ScatteredDrifter/Monorail-cut/pcb_source/Monorail_Steam_Reduced.kicad_sch

## KiCad design pcb_source/Monorail_Steam_Reduced.kicad_sch (2023-11-18)

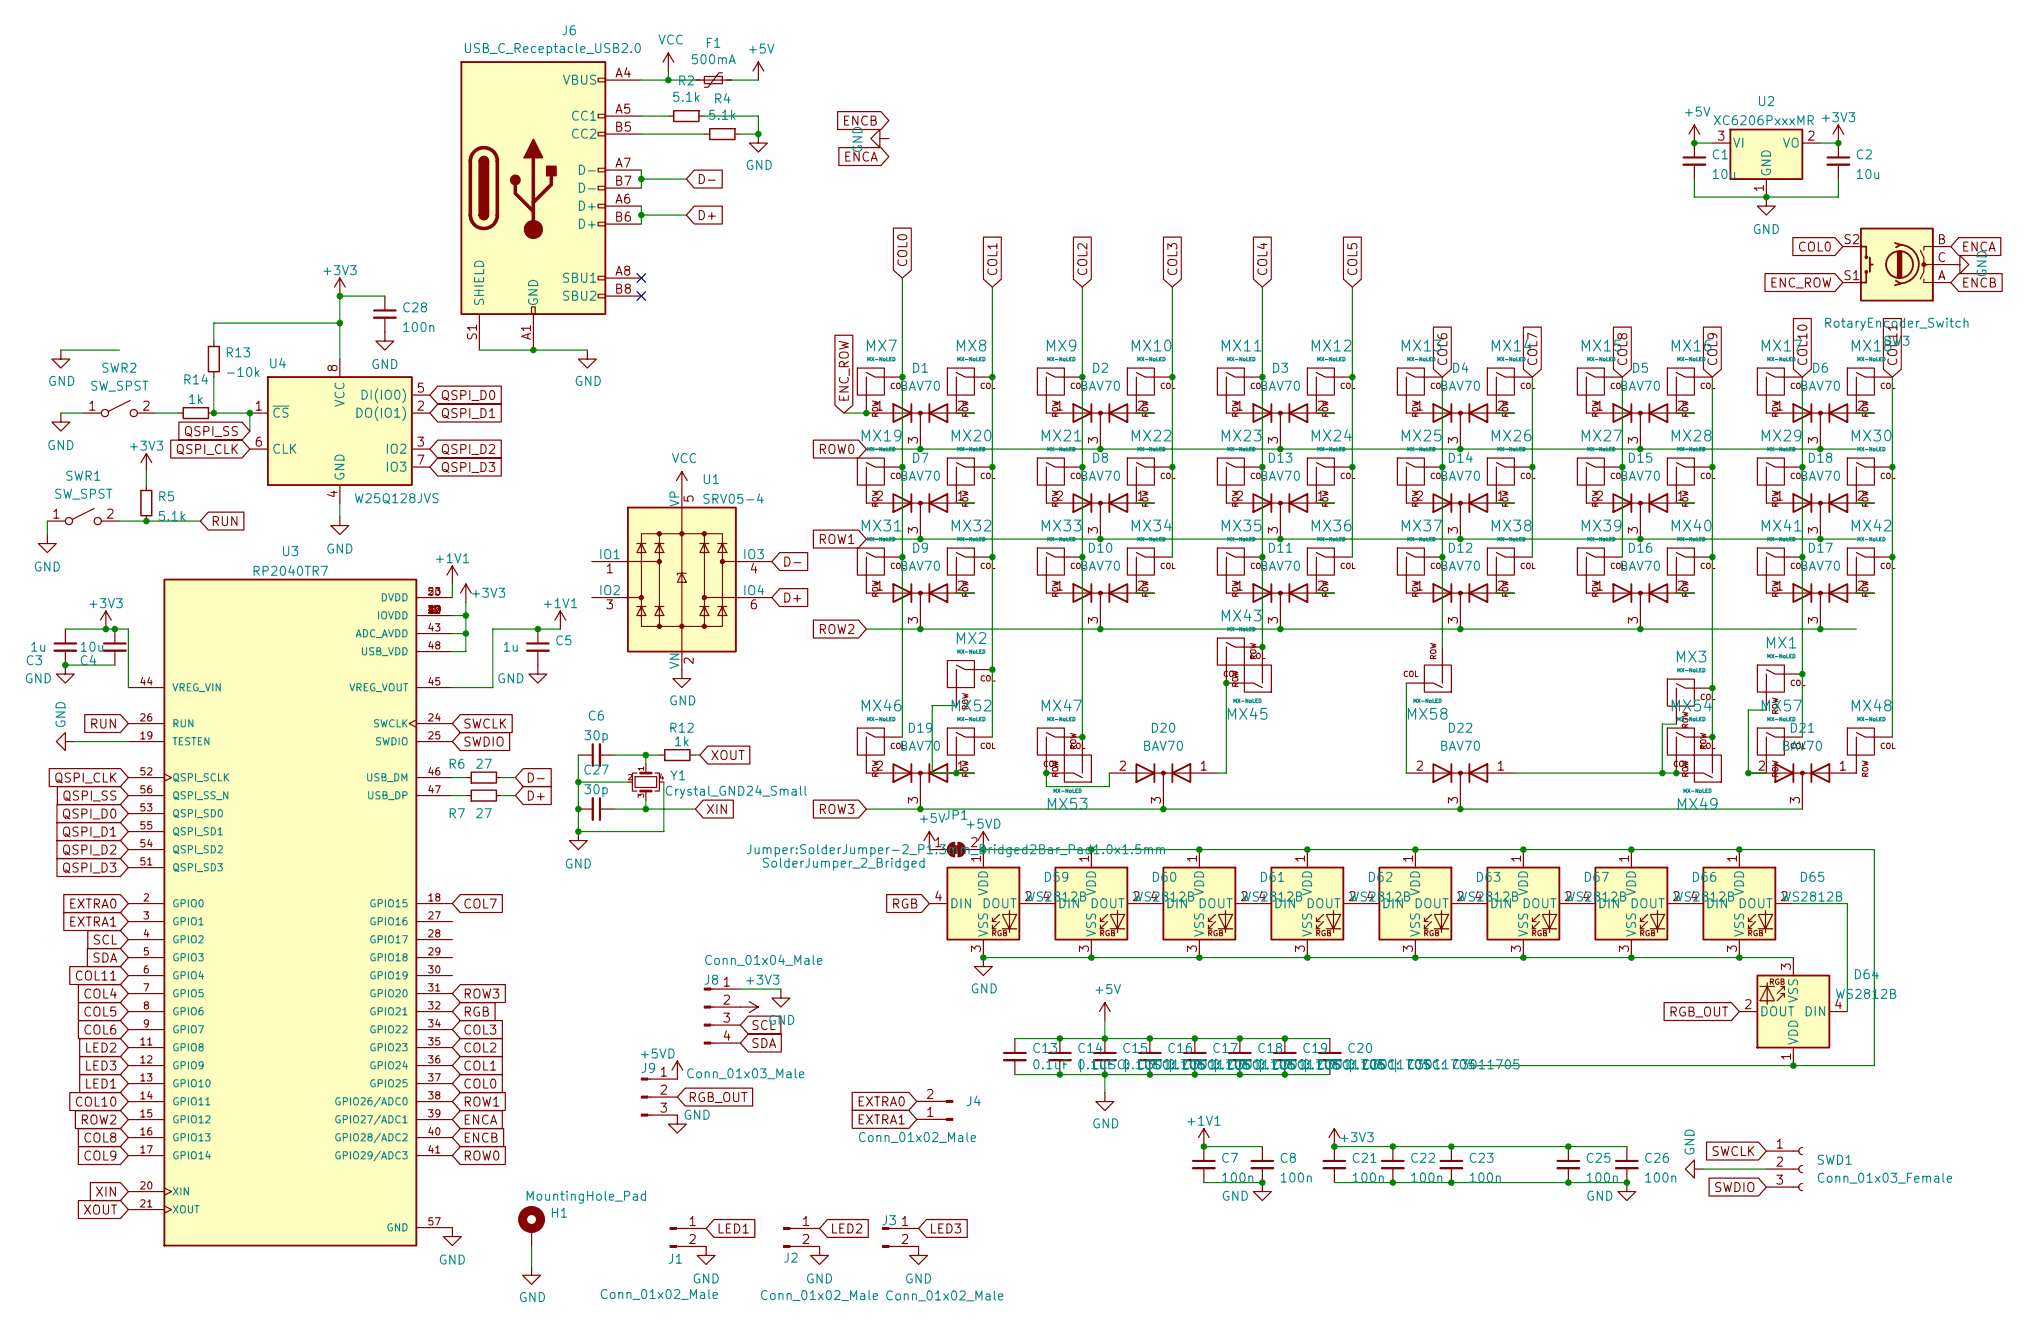
[picture p3: schematic Monorail_Steam_Reduced.kicad_sch]

Parts:
C1, C2, C4: 10u; C_0402_1005Metric; LCSC C315248
C3, C5: 1u; C_0402_1005Metric; LCSC C107372
C6, C27: 30p; C_0402_1005Metric; LCSC C1570
C7, C8, C21, C22, C23, C25, C26, C28: 100n; C_0402_1005Metric; LCSC C60474
C13, C14, C15, C16, C17, C18, C19, C20: 0.1uF | LCSC: C3011705; C_0603_1608Metric; LCSC C3011705
D1, D2, D3, D4, D5, D6, D7, D8, D9, D10, D11, D12, D13, D14, D15, D16, D17, D18, D19, D20, D21, D22: BAV70; SOT-23; LCSC C68978
D59, D60, D61, D62, D63, D64, D65, D66, D67: WS2812B; WS2812B_data-bridgeable
F1: 500mA; Fuse_1206_3216Metric; LCSC C69688
H1: MountingHole_Pad; Minivan-reference
J1, J2, J3: Conn_01x02_Male; PinHeader_1x02_P2.54mm_Vertical
J4: Conn_01x02_Male; PinSocket_1x02_P2.54mm_Vertical
J6: USB_C_Receptacle_USB2.0; USB_C_Receptacle_HRO_TYPE-C-31-M-12; LCSC C165948
J8: Conn_01x04_Male; PinHeader_1x04_P2.54mm_Vertical
J9: Conn_01x03_Male; PinHeader_1x03_P2.54mm_Vertical
JP1: SolderJumper_2_Bridged; SolderJumper-2_P1.3mm_Bridged2Bar_Pad1.0x1.5mm
MX1, MX2, MX7, MX8, MX9, MX10, MX11, MX12, MX13, MX14, MX15, MX16, MX17, MX18, MX19, MX20, MX21, MX22, MX23, MX24, MX25, MX26, MX27, MX28, MX29, MX30, MX31, MX32, MX33, MX34, MX35, MX36, MX37, MX38, MX39, MX40, MX41, MX42, MX43, MX45, MX46, MX47, MX48, MX49, MX52, MX53, MX54, MX57, MX58: MX-NoLED; SW_MX_HS_1u_NOREF
MX3: MX-NoLED; SW_MX_1u
R2, R4, R5: 5.1k; R_0603_1608Metric; LCSC C23186
R6, R7: 27; R_0402_1005Metric; LCSC C138021
R12, R14: 1k; R_0402_1005Metric; LCSC C11702
R13: -10k; R_0603_1608Metric; LCSC C98220
SW3: RotaryEncoder_Switch; ROT_Alps_EC11E-Switch
SWD1: Conn_01x03_Female; PinHeader_1x03_P2.54mm_Vertical
SWR1, SWR2: SW_SPST; SW_SPST_TL3342; LCSC C2886894
U1: SRV05-4; SOT-23-6; LCSC C85364
U2: XC6206PxxxMR; SOT-23; LCSC C5446
U3: RP2040TR7; RP2040-QFN-56; PARTREV 1.7.1; LCSC C2040
U4: W25Q128JVS; SOIC-8_5.23x5.23mm_P1.27mm; LCSC C97521
Y1: Crystal_GND24_Small; Crystal_SMD_3225-4Pin_3.2x2.5mm; LCSC C9002

Connections:
+1V1: C5.1, C7.1, C8.1, U3.23 (DVDD), U3.45 (VREG_VOUT), U3.50 (DVDD)
+3V3: C2.1, C3.1, C4.1, C21.1, C22.1, C23.1, C25.1, C26.1, C28.1, J8.2, R5.1, R13.1, U2.2 (VO), U3.1 (IOVDD), U3.10 (IOVDD), U3.22 (IOVDD), U3.33 (IOVDD), U3.42 (IOVDD), U3.43 (ADC_AVDD), U3.44 (VREG_VIN), U3.48 (USB_VDD), U3.49 (IOVDD), U4.8 (VCC)
+5V: C1.1, C13.1, C14.1, C15.1, C16.1, C17.1, C18.1, C19.1, C20.1, F1.1, JP1.1 (A), U2.3 (VI)
+5VD: D59.1 (VDD), D60.1 (VDD), D61.1 (VDD), D62.1 (VDD), D63.1 (VDD), D64.1 (VDD), D65.1 (VDD), D66.1 (VDD), D67.1 (VDD), J9.1, JP1.2 (B)
COL0: MX7.1 (COL), MX19.1 (COL), MX31.1 (COL), MX46.1 (COL), SW3.S2, U3.37 (GPIO25)
COL1: MX2.1 (COL), MX8.1 (COL), MX20.1 (COL), MX32.1 (COL), MX52.1 (COL), U3.36 (GPIO24)
COL2: MX9.1 (COL), MX21.1 (COL), MX33.1 (COL), MX47.1 (COL), MX53.2 (ROW), U3.35 (GPIO23)
COL3: MX10.1 (COL), MX22.1 (COL), MX34.1 (COL), U3.34 (GPIO22)
COL4: MX11.1 (COL), MX23.1 (COL), MX35.1 (COL), MX43.1 (COL), MX45.2 (ROW), U3.7 (GPIO5)
COL5: MX12.1 (COL), MX24.1 (COL), MX36.1 (COL), U3.8 (GPIO6)
COL6: MX13.1 (COL), MX25.1 (COL), MX37.1 (COL), MX58.2 (ROW), U3.9 (GPIO7)
COL7: MX14.1 (COL), MX26.1 (COL), MX38.1 (COL), U3.18 (GPIO15)
COL8: MX15.1 (COL), MX27.1 (COL), MX39.1 (COL), U3.16 (GPIO13)
COL9: MX3.1 (COL), MX16.1 (COL), MX28.1 (COL), MX40.1 (COL), MX49.2 (ROW), MX54.1 (COL), U3.17 (GPIO14)
COL10: MX1.1 (COL), MX17.1 (COL), MX29.1 (COL), MX41.1 (COL), MX57.1 (COL), U3.14 (GPIO11)
COL11: MX18.1 (COL), MX30.1 (COL), MX42.1 (COL), MX48.1 (COL), U3.6 (GPIO4)
D+: J6.A6 (D+), J6.B6 (D+), R7.2, U1.6 (IO4)
D-: J6.A7 (D-), J6.B7 (D-), R6.2, U1.4 (IO3)
ENCA: SW3.B, U3.39 (GPIO27/ADC1)
ENCB: SW3.A, U3.40 (GPIO28/ADC2)
ENC_ROW: D1.1 (A), MX7.2 (ROW), SW3.S1
EXTRA0: J4.2, U3.2 (GPIO0)
EXTRA1: J4.1, U3.3 (GPIO1)
GND: C1.2, C2.2, C3.2, C4.2, C5.2, C6.1, C7.2, C8.2, C13.2, C14.2, C15.2, C16.2, C17.2, C18.2, C19.2, C20.2, C21.2, C22.2, C23.2, C25.2, C26.2, C27.2, C28.2, D59.3 (VSS), D60.3 (VSS), D61.3 (VSS), D62.3 (VSS), D63.3 (VSS), D64.3 (VSS), D65.3 (VSS), D66.3 (VSS), D67.3 (VSS), H1.1, J1.2, J2.2, J3.2, J6.A1 (GND), J6.A12 (GND), J6.B1 (GND), J6.B12 (GND), J6.S1 (SHIELD), J8.1, J9.3, R2.1, R4.1, SW3.C, SWD1.2, SWR1.1 (A), SWR2.1 (A), U1.2 (VN), U2.1 (GND), U3.19 (TESTEN), U3.57 (GND), U4.4 (GND), Y1.2, Y1.4
LED1: J1.1, U3.13 (GPIO10)
LED2: J2.1, U3.11 (GPIO8)
LED3: J3.1, U3.12 (GPIO9)
unnamed: C6.2, R12.1, Y1.1
unnamed: D1.2 (A), MX8.2 (ROW)
unnamed: D2.1 (A), MX9.2 (ROW)
unnamed: D2.2 (A), MX10.2 (ROW)
unnamed: D3.1 (A), MX11.2 (ROW)
unnamed: D3.2 (A), MX12.2 (ROW)
unnamed: D4.1 (A), MX13.2 (ROW)
unnamed: D4.2 (A), MX14.2 (ROW)
unnamed: D5.1 (A), MX15.2 (ROW)
unnamed: D5.2 (A), MX16.2 (ROW)
unnamed: D6.1 (A), MX17.2 (ROW)
unnamed: D6.2 (A), MX18.2 (ROW)
unnamed: D7.1 (A), MX20.2 (ROW)
unnamed: D7.2 (A), MX19.2 (ROW)
unnamed: D8.1 (A), MX22.2 (ROW)
unnamed: D8.2 (A), MX21.2 (ROW)
unnamed: D9.1 (A), MX31.2 (ROW)
unnamed: D9.2 (A), MX32.2 (ROW)
unnamed: D10.1 (A), MX33.2 (ROW)
unnamed: D10.2 (A), MX34.2 (ROW)
unnamed: D11.1 (A), MX35.2 (ROW)
unnamed: D11.2 (A), MX36.2 (ROW)
unnamed: D12.1 (A), MX37.2 (ROW)
unnamed: D12.2 (A), MX38.2 (ROW)
unnamed: D13.1 (A), MX24.2 (ROW)
unnamed: D13.2 (A), MX23.2 (ROW)
unnamed: D14.1 (A), MX26.2 (ROW)
unnamed: D14.2 (A), MX25.2 (ROW)
unnamed: D15.1 (A), MX28.2 (ROW)
unnamed: D15.2 (A), MX27.2 (ROW)
unnamed: D16.1 (A), MX39.2 (ROW)
unnamed: D16.2 (A), MX40.2 (ROW)
unnamed: D17.1 (A), MX41.2 (ROW)
unnamed: D17.2 (A), MX42.2 (ROW)
unnamed: D18.1 (A), MX29.2 (ROW)
unnamed: D18.2 (A), MX30.2 (ROW)
unnamed: D19.1 (A), MX2.2 (ROW), MX52.2 (ROW)
unnamed: D19.2 (A), MX46.2 (ROW)
unnamed: D20.1 (A), MX43.2 (ROW), MX45.1 (COL)
unnamed: D20.2 (A), MX47.2 (ROW), MX53.1 (COL)
unnamed: D21.1 (A), MX48.2 (ROW)
unnamed: D21.2 (A), MX1.2 (ROW), MX57.2 (ROW)
unnamed: D22.1 (A), MX3.2 (ROW), MX49.1 (COL), MX54.2 (ROW)
unnamed: D22.2 (A), MX58.1 (COL)
unnamed: D59.2 (DOUT), D60.4 (DIN)
unnamed: D60.2 (DOUT), D61.4 (DIN)
unnamed: D61.2 (DOUT), D62.4 (DIN)
unnamed: D62.2 (DOUT), D63.4 (DIN)
unnamed: D63.2 (DOUT), D67.4 (DIN)
unnamed: D64.4 (DIN), D65.2 (DOUT)
unnamed: D65.4 (DIN), D66.2 (DOUT)
unnamed: D66.4 (DIN), D67.2 (DOUT)
unnamed: J6.A5 (CC1), R2.2
unnamed: J6.B5 (CC2), R4.2
unnamed: R6.1, U3.46 (USB_DM)
unnamed: R7.1, U3.47 (USB_DP)
unnamed: R14.2, SWR2.2 (B)
QSPI_CLK: U3.52 (QSPI_SCLK), U4.6 (CLK)
QSPI_D0: U3.53 (QSPI_SD0), U4.5 (DI(IO0))
QSPI_D1: U3.55 (QSPI_SD1), U4.2 (DO(IO1))
QSPI_D2: U3.54 (QSPI_SD2), U4.3 (IO2)
QSPI_D3: U3.51 (QSPI_SD3), U4.7 (IO3)
QSPI_SS: R13.2, R14.1, U3.56 (QSPI_SS_N), U4.1 (~CS)
RGB: D59.4 (DIN), U3.32 (GPIO21)
RGB_OUT: D64.2 (DOUT), J9.2
ROW0: D1.3 (K), D2.3 (K), D3.3 (K), D4.3 (K), D5.3 (K), D6.3 (K), U3.41 (GPIO29/ADC3)
ROW1: D7.3 (K), D8.3 (K), D13.3 (K), D14.3 (K), D15.3 (K), D18.3 (K), U3.38 (GPIO26/ADC0)
ROW2: D9.3 (K), D10.3 (K), D11.3 (K), D12.3 (K), D16.3 (K), D17.3 (K), U3.15 (GPIO12)
ROW3: D19.3 (K), D20.3 (K), D21.3 (K), D22.3 (K), U3.31 (GPIO20)
RUN: R5.2, SWR1.2 (B), U3.26 (RUN)
SCL: J8.3, U3.4 (GPIO2)
SDA: J8.4, U3.5 (GPIO3)
SWCLK: SWD1.1, U3.24 (SWCLK)
SWDIO: SWD1.3, U3.25 (SWDIO)
VCC: F1.2, J6.A4 (VBUS), J6.A9 (VBUS), J6.B4 (VBUS), J6.B9 (VBUS), U1.5 (VP)
XIN: C27.1, U3.20 (XIN), Y1.3
XOUT: R12.2, U3.21 (XOUT)
